ivica3730k/DevIcE-Dev-Board/New-IoT-Product-master/schematic.sch

## EAGLE design New-IoT-Product-master/schematic.sch (2019-11-18)

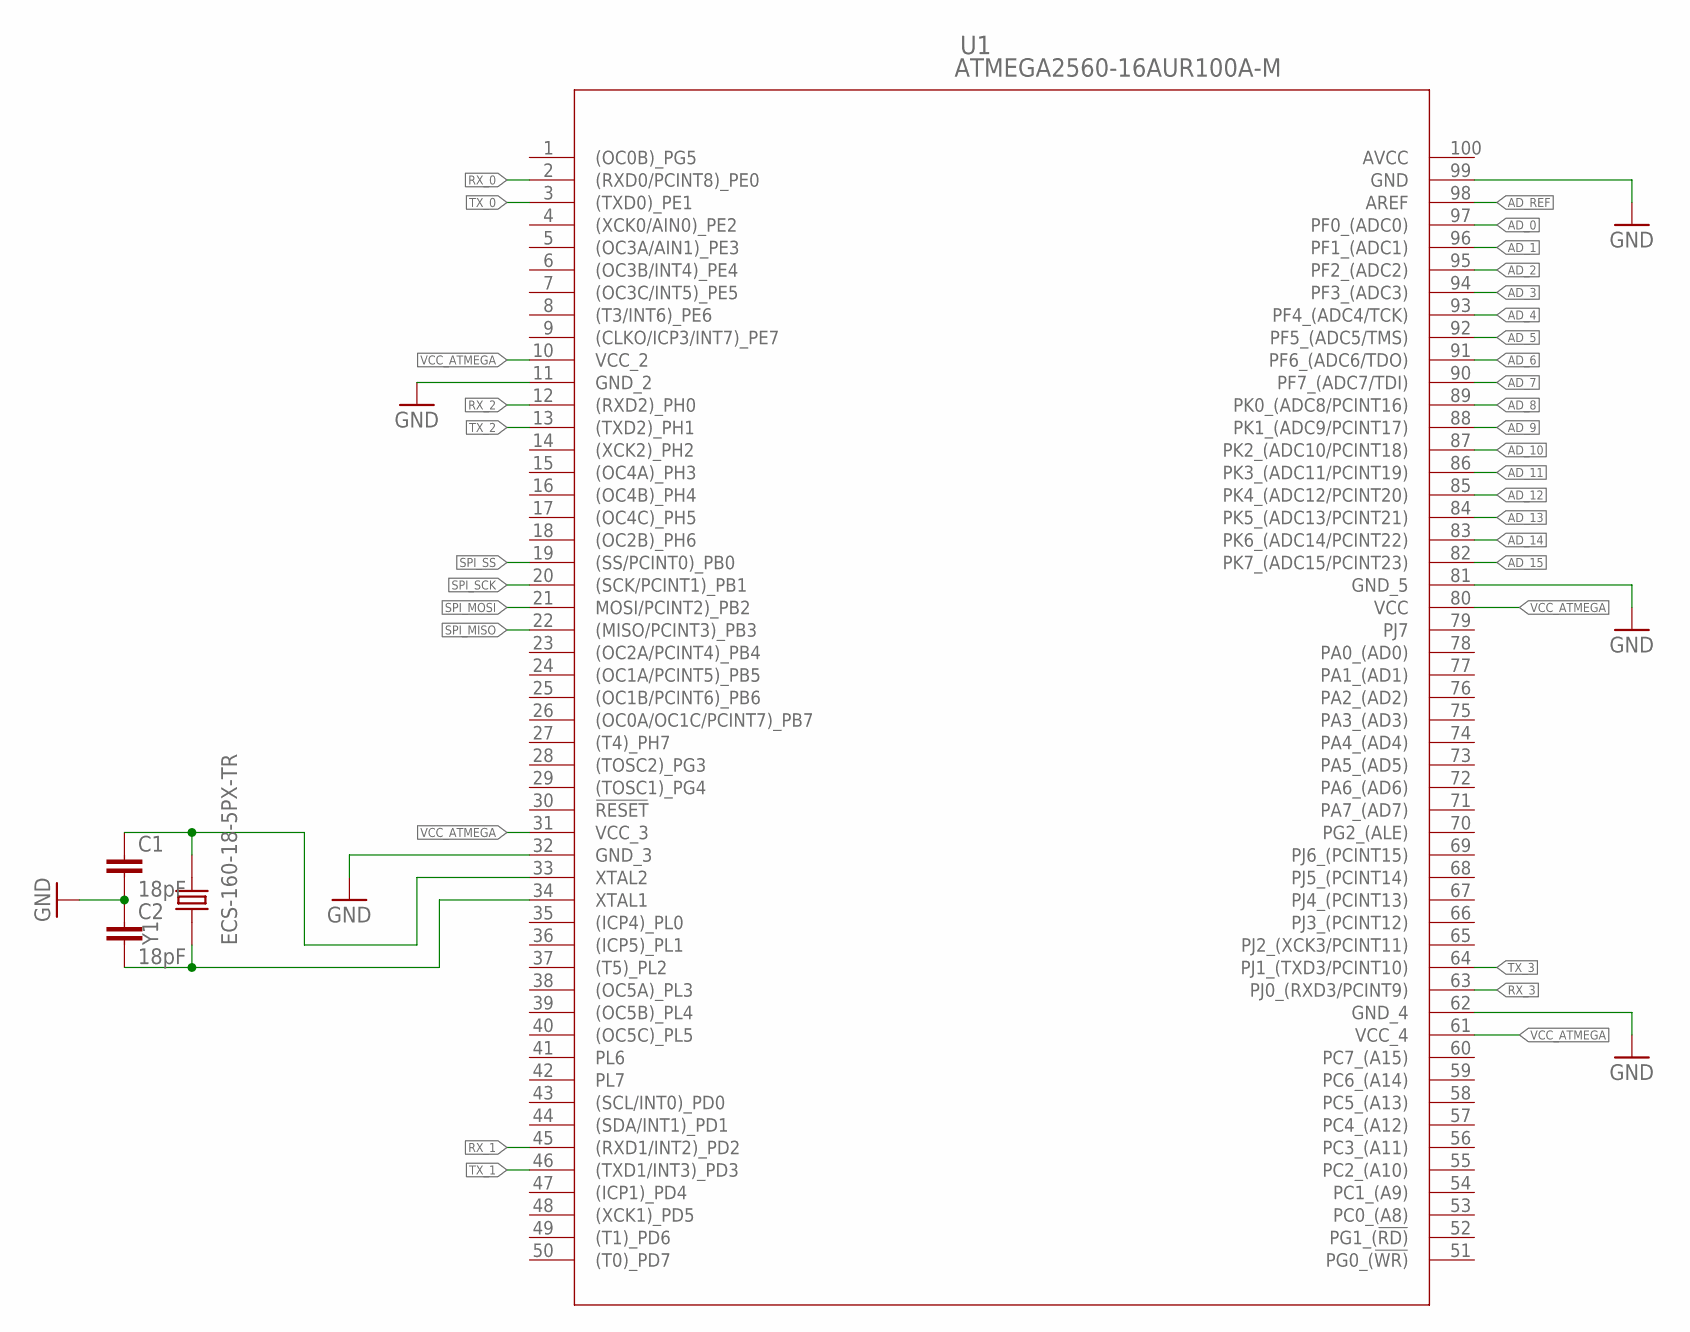
[picture p9: schematic schematic.sch]

Parts:
C1, C2: 18pF; C0603
U1: ATMEGA2560-16AUR100A-M; 100A-M
Y1: ECS-160-18-5PX-TR; XTAL_ECS-160-18-5PX-TR

Connections:
AD_0: U1.97 (PF0_(ADC0))
AD_1: U1.96 (PF1_(ADC1))
AD_2: U1.95 (PF2_(ADC2))
AD_3: U1.94 (PF3_(ADC3))
AD_4: U1.93 (PF4_(ADC4/TCK))
AD_5: U1.92 (PF5_(ADC5/TMS))
AD_6: U1.91 (PF6_(ADC6/TDO))
AD_7: U1.90 (PF7_(ADC7/TDI))
AD_8: U1.89 (PK0_(ADC8/PCINT16))
AD_9: U1.88 (PK1_(ADC9/PCINT17))
AD_10: U1.87 (PK2_(ADC10/PCINT18))
AD_11: U1.86 (PK3_(ADC11/PCINT19))
AD_12: U1.85 (PK4_(ADC12/PCINT20))
AD_13: U1.84 (PK5_(ADC13/PCINT21))
AD_14: U1.83 (PK6_(ADC14/PCINT22))
AD_15: U1.82 (PK7_(ADC15/PCINT23))
AD_REF: U1.98 (AREF)
GND: C1.2, C2.1, U1.11 (GND_2), U1.32 (GND_3), U1.62 (GND_4), U1.81 (GND_5), U1.99 (GND)
unnamed: C1.1, U1.33 (XTAL2), Y1.2
unnamed: C2.2, U1.34 (XTAL1), Y1.1
RX_0: U1.2 ((RXD0/PCINT8)_PE0)
RX_1: U1.45 ((RXD1/INT2)_PD2)
RX_2: U1.12 ((RXD2)_PH0)
RX_3: U1.63 (PJ0_(RXD3/PCINT9))
SPI_MISO: U1.22 ((MISO/PCINT3)_PB3)
SPI_MOSI: U1.21 (MOSI/PCINT2)_PB2)
SPI_SCK: U1.20 ((SCK/PCINT1)_PB1)
SPI_SS: U1.19 ((SS/PCINT0)_PB0)
TX_0: U1.3 ((TXD0)_PE1)
TX_1: U1.46 ((TXD1/INT3)_PD3)
TX_2: U1.13 ((TXD2)_PH1)
TX_3: U1.64 (PJ1_(TXD3/PCINT10))
VCC_ATMEGA: U1.10 (VCC_2), U1.31 (VCC_3), U1.61 (VCC_4), U1.80 (VCC)
